RaulMallorca/Estacion_metereologica/Esquemas/ADSWheather-NodeMCU_bb.png

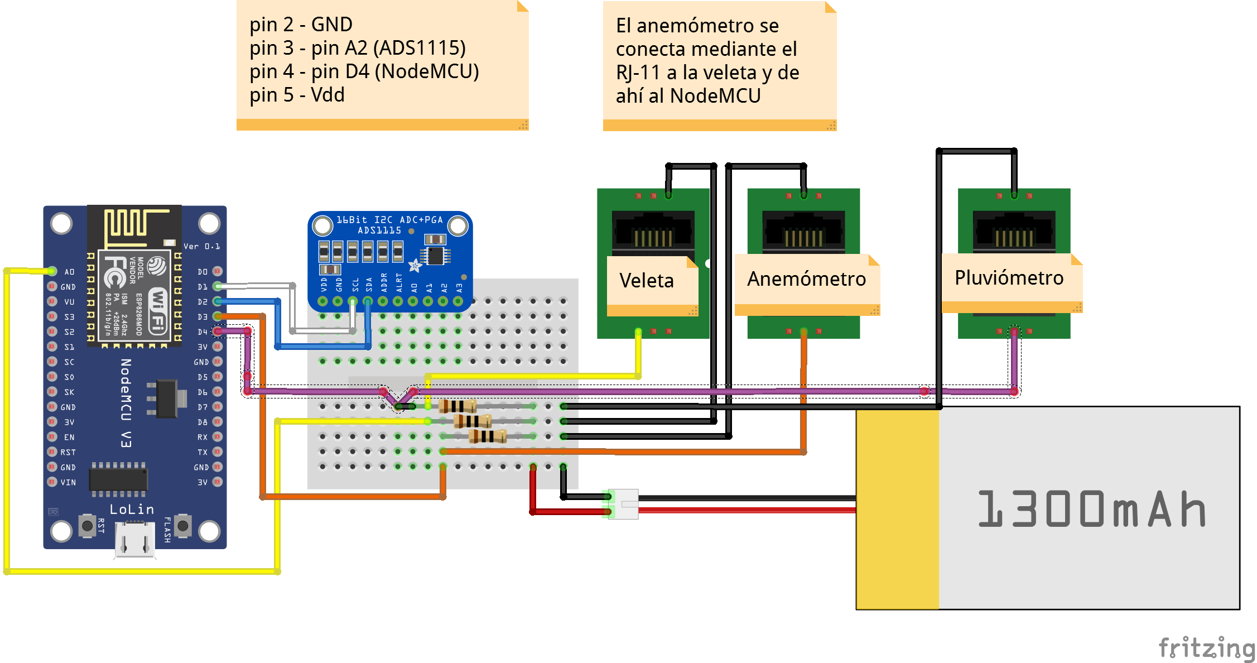
Esquemas/ADSWheather-NodeMCU_bb.png
