RaulMallorca/Estacion_metereologica/Esquemas/ADSWheather-NodeMCU_esquemático.png

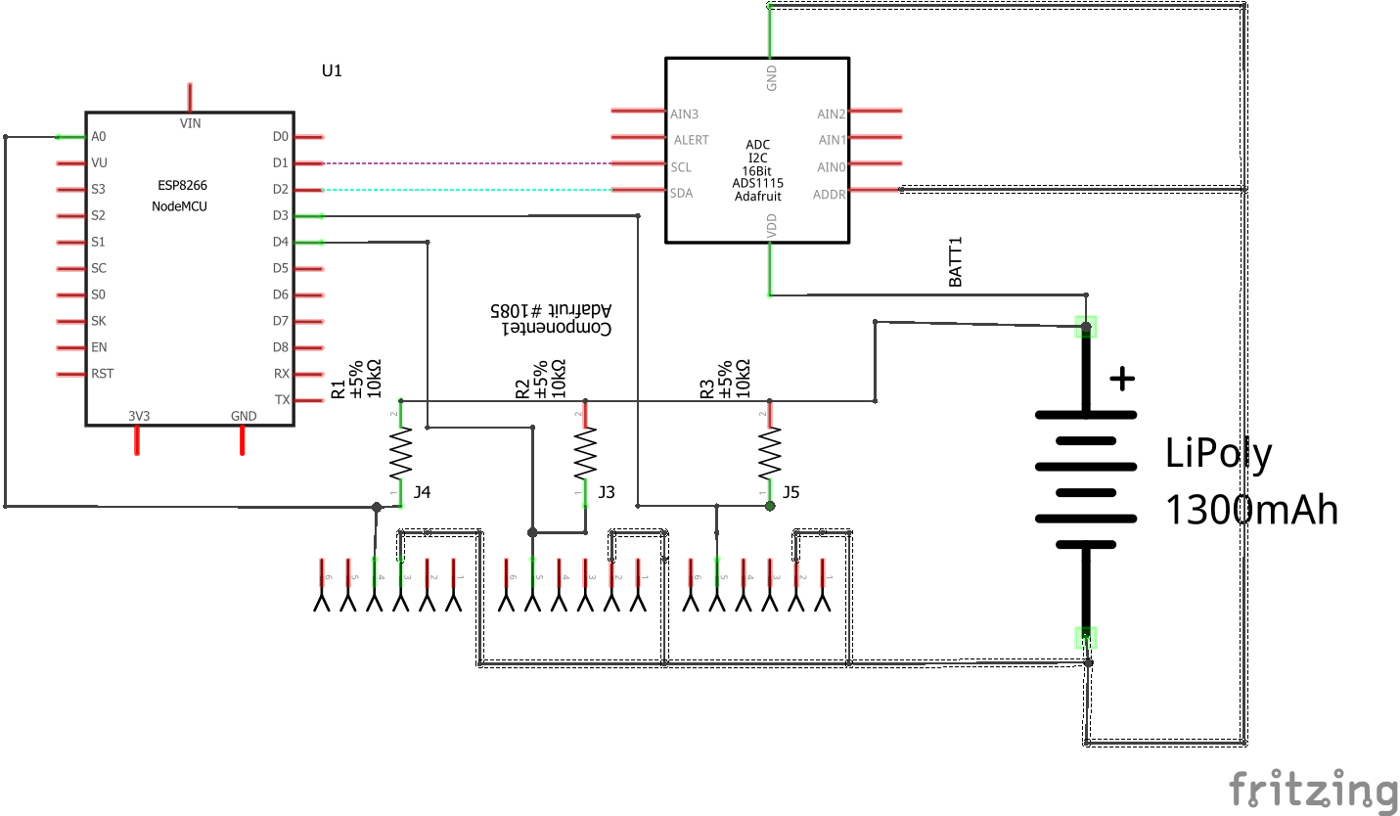
Esquemas/ADSWheather-NodeMCU_esquemático.png
