RaulMallorca/Estacion_metereologica/Esquemas/Anemometro_NodeMCU_bb.png

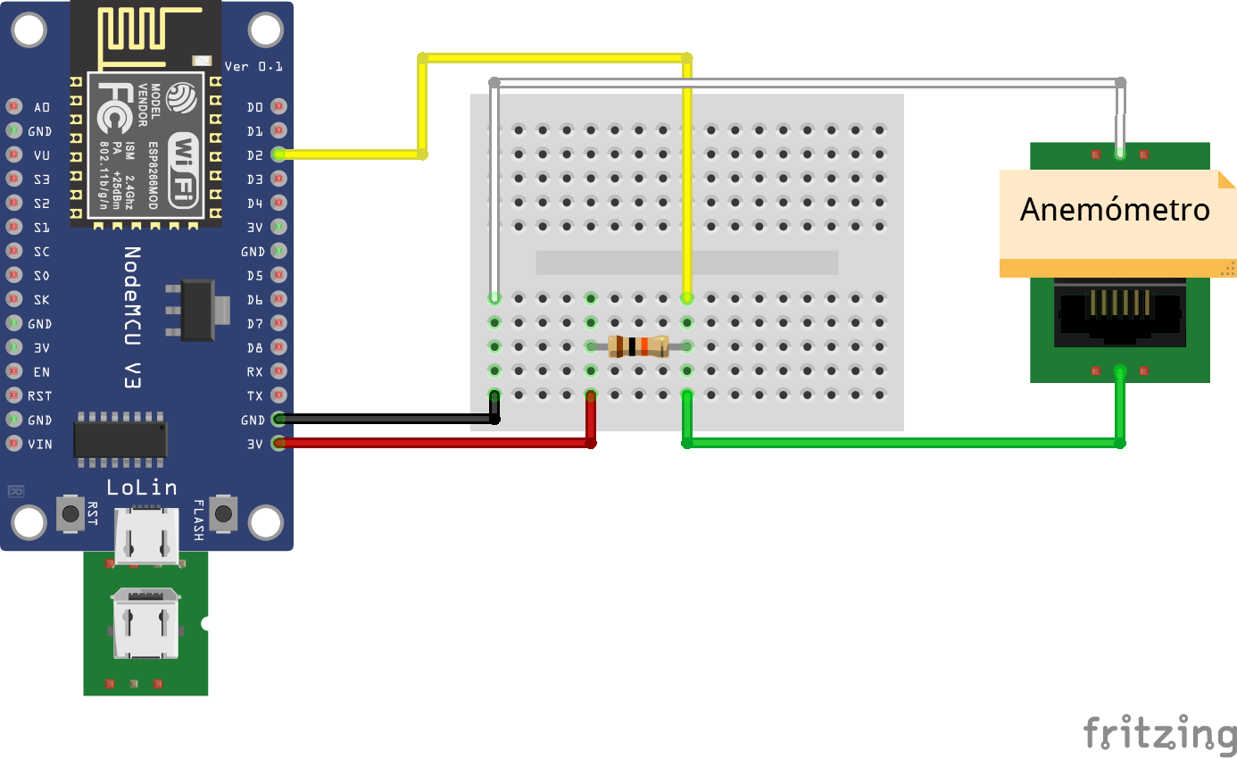
Esquemas/Anemometro_NodeMCU_bb.png
