RaulMallorca/Estacion_metereologica/Esquemas/NodeMCU-Servidor_bb.png

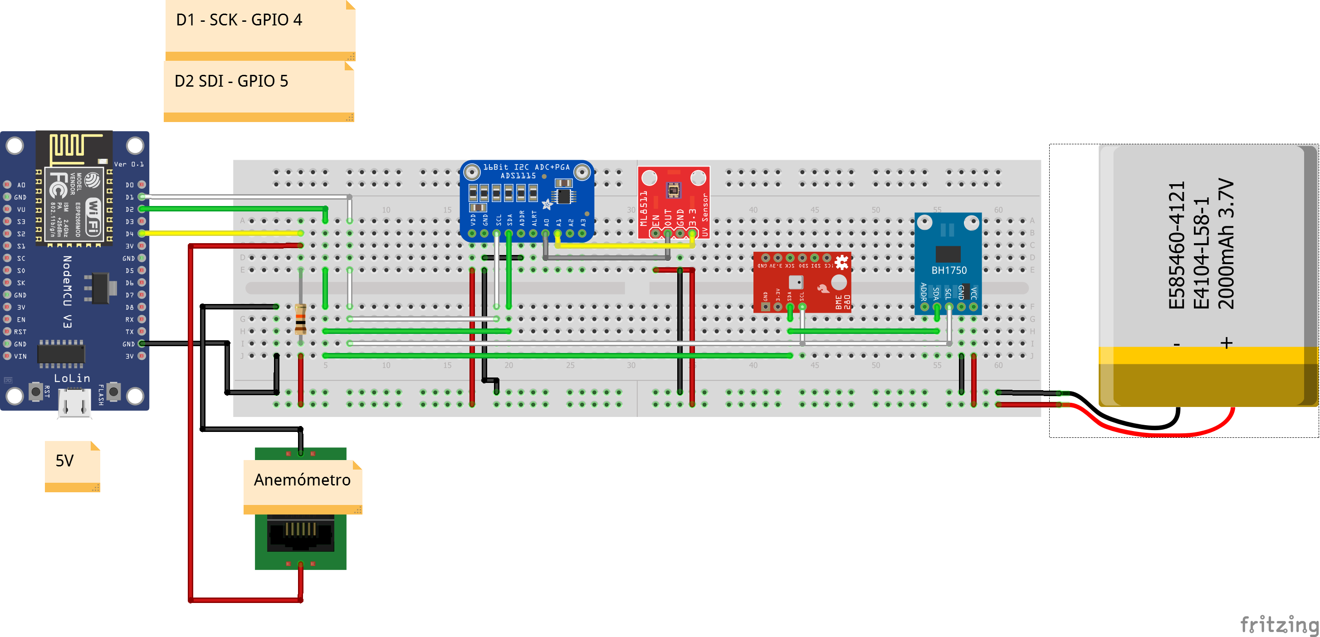
Esquemas/NodeMCU-Servidor_bb.png
