RaulMallorca/Estacion_metereologica/Sensores/ML8511_ADS1115ADC/ml8511-uv GITHUB.jpg

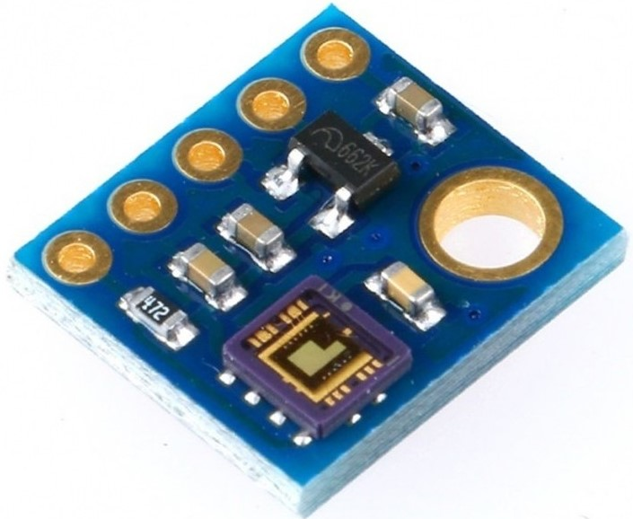
Sensores/ML8511_ADS1115ADC/ml8511-uv GITHUB.jpg
